marknarain/digital-full-adder/74HC00/KiCad/circuit-diagramm.kicad_sch

## KiCad design 74HC00/KiCad/circuit-diagramm.kicad_sch (2024-01-19)

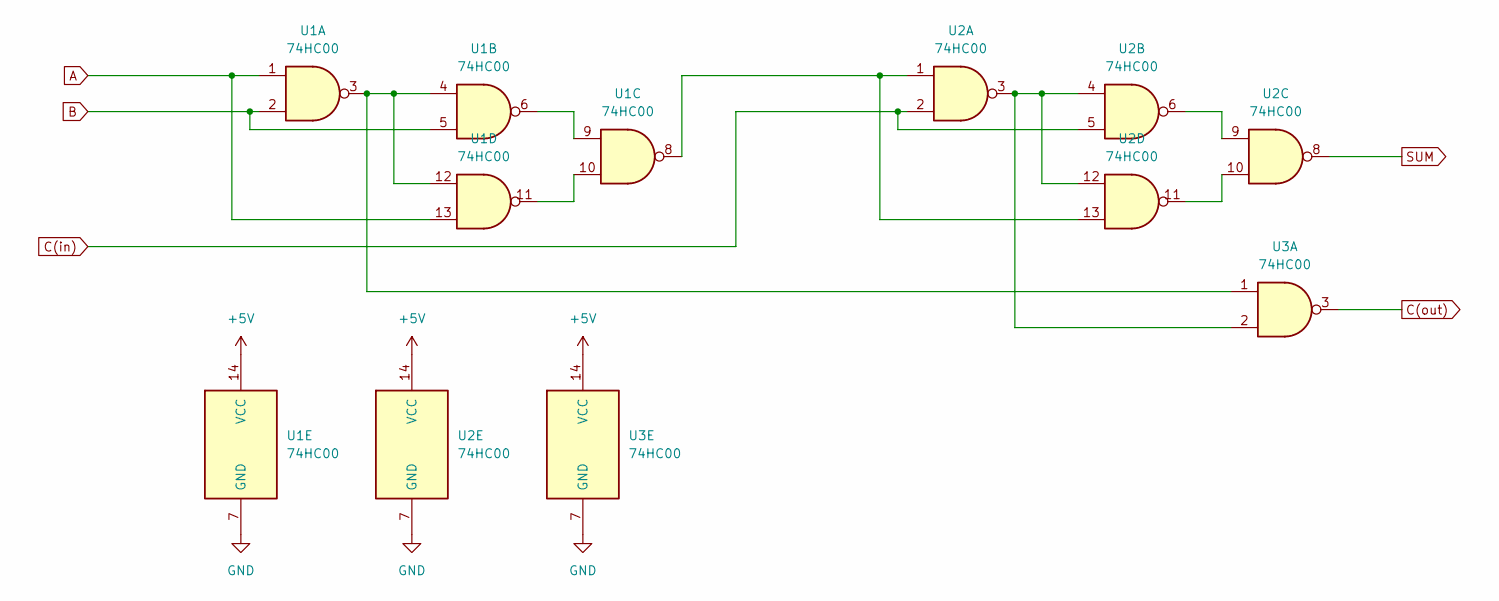
[picture p15: schematic circuit-diagramm.kicad_sch]

Parts:
U1, U2, U3: 74HC00

Connections:
+5V: U1.14 (VCC), U2.14 (VCC), U3.14 (VCC)
A: U1.1, U1.13
B: U1.2, U1.5
C(in): U2.2, U2.5
C(out): U3.3
GND: U1.7 (GND), U2.7 (GND), U3.7 (GND)
unnamed: U1.6, U1.9
unnamed: U1.8, U2.1, U2.13
unnamed: U1.10, U1.11
unnamed: U1.3, U1.4, U1.12, U3.1
unnamed: U2.6, U2.9
unnamed: U2.10, U2.11
unnamed: U2.3, U2.4, U2.12, U3.2
SUM: U2.8
