marknarain/digital-full-adder/Power supply/KiCad/circuit-diagram.kicad_sch

## KiCad design Power supply/KiCad/circuit-diagram.kicad_sch (2024-01-19)

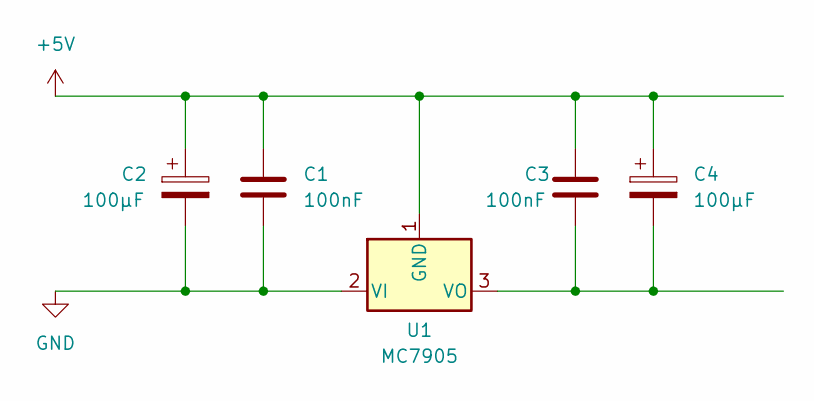
[picture p16: schematic circuit-diagram.kicad_sch]

Parts:
C1, C3: 100nF
C2, C4: 100µF
U1: MC7905

Connections:
+5V: C1.1, C2.1, C3.1, C4.1, U1.1 (GND)
GND: C1.2, C2.2, U1.2 (VI)
unnamed: C3.2, C4.2, U1.3 (VO)
