marknarain/digital-full-adder/Transistors/KiCad/circuit-diagramm.kicad_sch

## KiCad design Transistors/KiCad/circuit-diagramm.kicad_sch (2023-12-22)

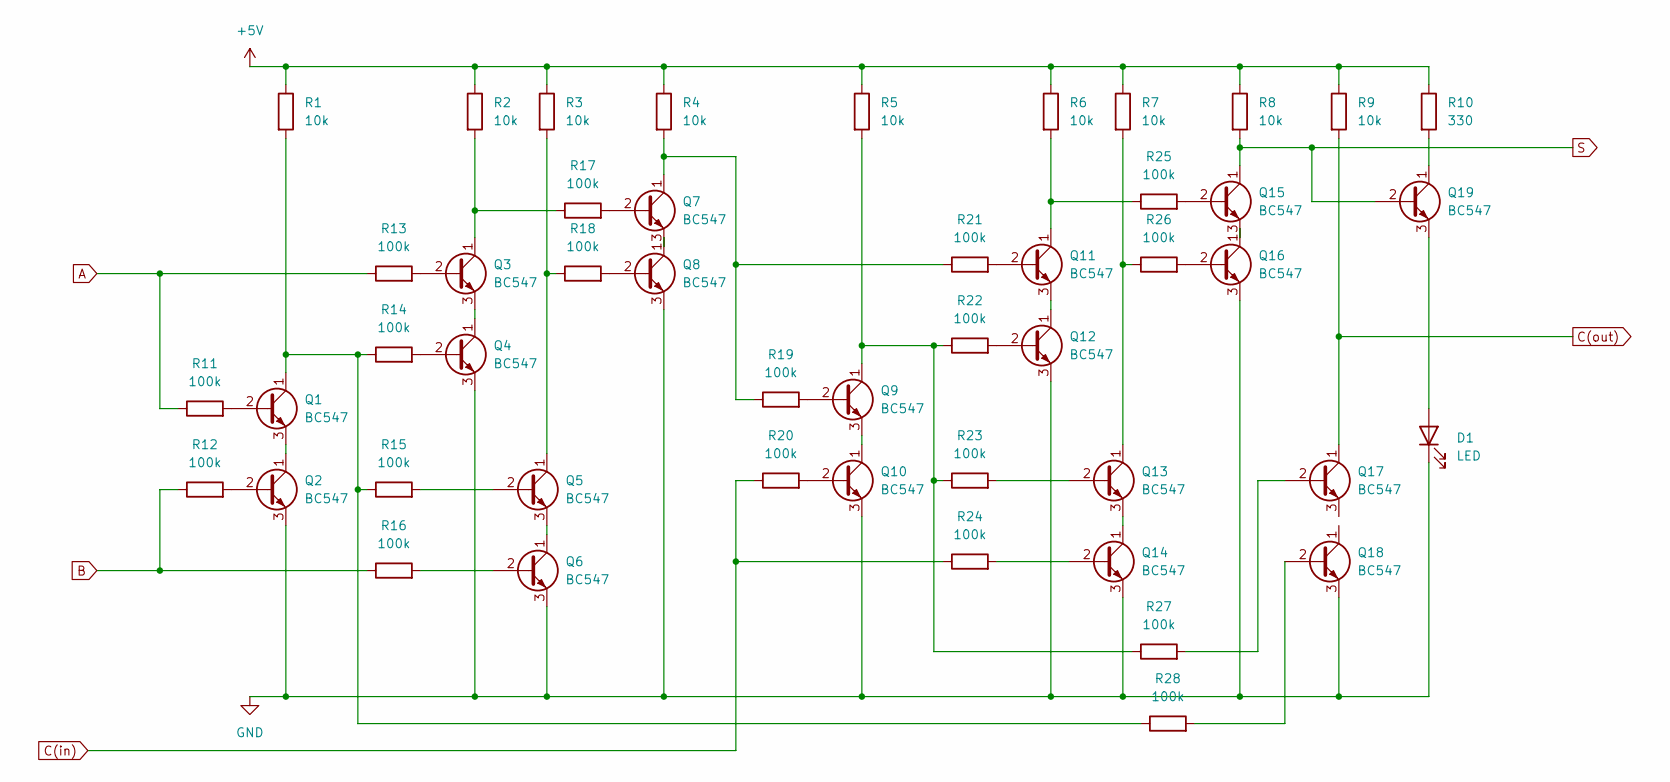
[picture p17: schematic circuit-diagramm.kicad_sch]

Parts:
D1: LED
Q1, Q2, Q3, Q4, Q5, Q6, Q7, Q8, Q9, Q10, Q11, Q12, Q13, Q14, Q15, Q16, Q17, Q18, Q19: BC547; TO-92_Inline
R1, R2, R3, R4, R5, R6, R7, R8, R9: 10k
R10: 330
R11, R12, R13, R14, R15, R16, R17, R18, R19, R20, R21, R22, R23, R24, R25, R26, R27, R28: 100k

Connections:
+5V: R1.1, R2.1, R3.1, R4.1, R5.1, R6.1, R7.1, R8.1, R9.1, R10.1
A: R11.1, R13.1
B: R12.1, R16.1
C(in): R20.1, R24.1
C(out): Q17.1 (C), R9.2
GND: D1.1 (K), Q2.3 (E), Q4.3 (E), Q6.3 (E), Q8.3 (E), Q10.3 (E), Q12.3 (E), Q14.3 (E), Q16.3 (E), Q18.3 (E)
unnamed: D1.2 (A), Q19.3 (E)
unnamed: Q1.1 (C), R1.2, R14.1, R15.1, R28.1
unnamed: Q1.2 (B), R11.2
unnamed: Q1.3 (E), Q2.1 (C)
unnamed: Q2.2 (B), R12.2
unnamed: Q3.1 (C), R2.2, R17.1
unnamed: Q3.2 (B), R13.2
unnamed: Q3.3 (E), Q4.1 (C)
unnamed: Q4.2 (B), R14.2
unnamed: Q5.1 (C), R3.2, R18.1
unnamed: Q5.2 (B), R15.2
unnamed: Q5.3 (E), Q6.1 (C)
unnamed: Q6.2 (B), R16.2
unnamed: Q7.1 (C), R4.2, R19.1, R21.1
unnamed: Q7.2 (B), R17.2
unnamed: Q7.3 (E), Q8.1 (C)
unnamed: Q8.2 (B), R18.2
unnamed: Q9.1 (C), R5.2, R22.1, R23.1, R27.1
unnamed: Q9.2 (B), R19.2
unnamed: Q9.3 (E), Q10.1 (C)
unnamed: Q10.2 (B), R20.2
unnamed: Q11.1 (C), R6.2, R25.1
unnamed: Q11.2 (B), R21.2
unnamed: Q11.3 (E), Q12.1 (C)
unnamed: Q12.2 (B), R22.2
unnamed: Q13.1 (C), R7.2, R26.1
unnamed: Q13.2 (B), R23.2
unnamed: Q13.3 (E), Q14.1 (C)
unnamed: Q14.2 (B), R24.2
unnamed: Q15.2 (B), R25.2
unnamed: Q15.3 (E), Q16.1 (C)
unnamed: Q16.2 (B), R26.2
unnamed: Q17.2 (B), R27.2
unnamed: Q18.2 (B), R28.2
unnamed: Q19.1 (C), R10.2
S: Q15.1 (C), Q19.2 (B), R8.2
