marknarain/digital-full-adder/Transistors/KiCad/soldering.kicad_sch

## KiCad design Transistors/KiCad/soldering.kicad_sch (2023-12-22)

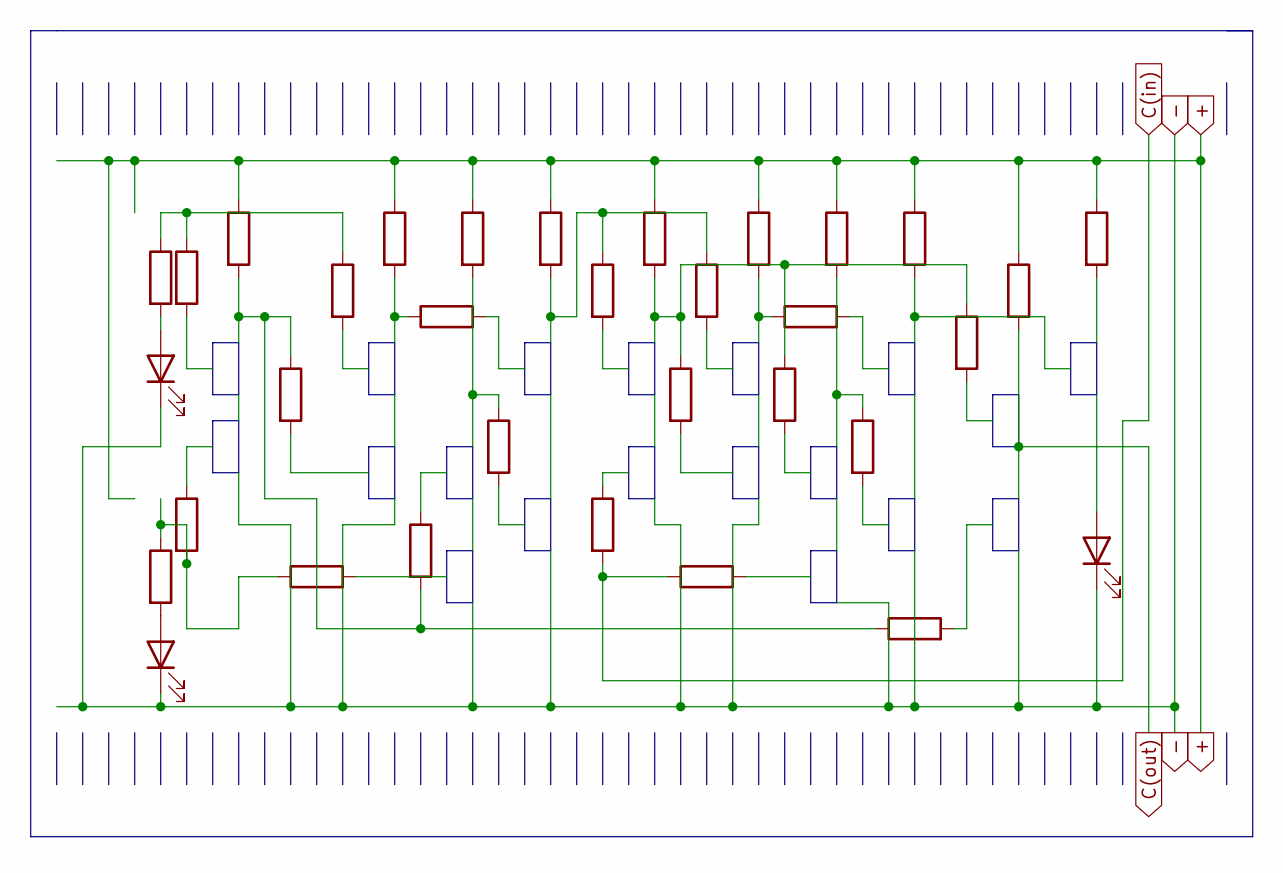
[picture p18: schematic soldering.kicad_sch]

Parts:
D1, D2, D3: LED
R1: 100k
R2, R3, R4, R5, R6, R7, R8, R9, R10, R17, R18, R19, R20, R21, R22, R23, R26, R27: R
R11, R12, R13, R14, R15, R16, R24, R25, R28, R29: 10k

Connections:
+: R1.1, R2.1, R3.1, R4.1, R5.1, R6.1, R7.1, R8.1, R9.1, R10.1
-: D1.1 (K), D2.1 (K), D3.1 (K)
C(in): R20.2, R24.1
C(out): R9.2
unnamed: D2.2 (A), R28.2
unnamed: D3.2 (A), R29.2
unnamed: R1.2, R9.1, R14.1, R15.2
unnamed: R11.1, R13.1, R28.1
unnamed: R12.2, R16.1, R29.1
unnamed: R2.2, R17.1
unnamed: R3.2, R18.1
unnamed: R4.2, R19.1, R21.1
unnamed: R5.2, R22.1, R23.1, R27.1
unnamed: R6.2, R25.1
unnamed: R7.2, R26.1
